kimf/zmk-config-olik/assets/keyboard-layout.png

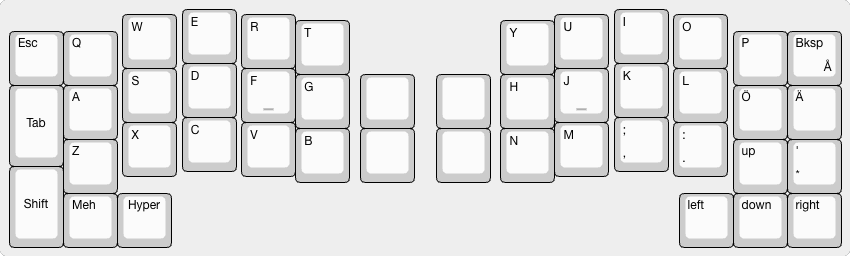
assets/keyboard-layout.png
