kimf/zmk-config-olik/assets/renders/7be2dbe0-a384-4cbd-b108-68b7f8a27338.PNG

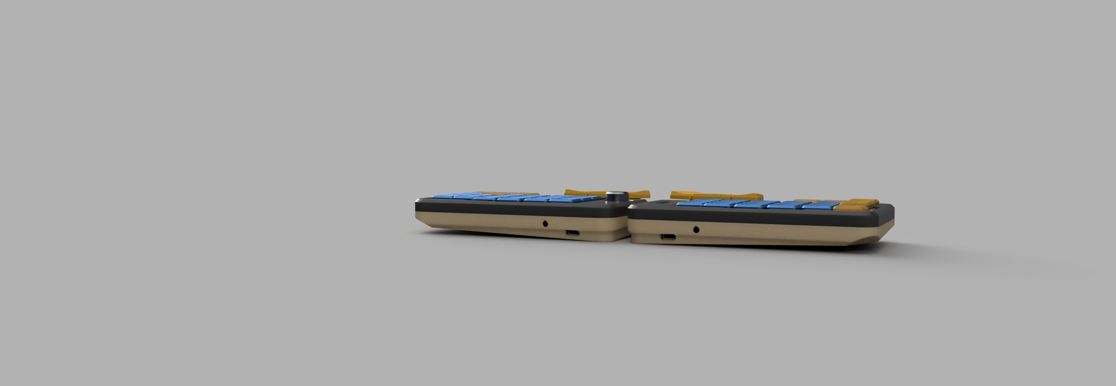
assets/renders/7be2dbe0-a384-4cbd-b108-68b7f8a27338.PNG
