kimf/zmk-config-olik/assets/stl/LeftBottom.stl

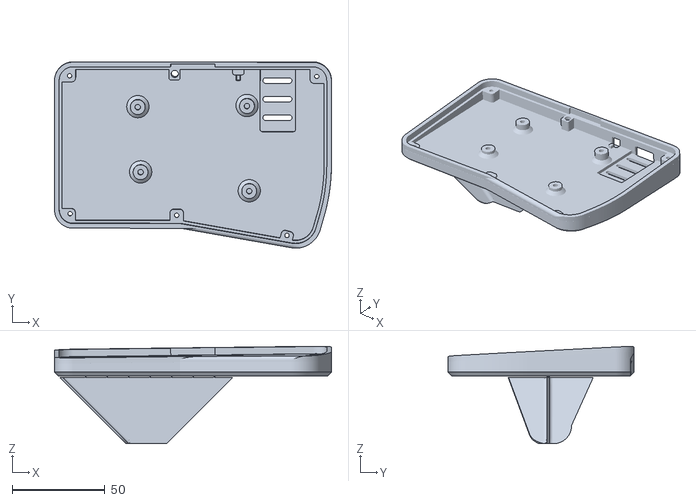
[picture p25: CAD file, 2026-02-03]
assets/stl/LeftBottom.stl
149.2 x 100.4 x 52.5
